SolderedElectronics/Dasduino-LITE-hardware-design/OUTPUTS/V1.2.2/Dasduino LITE Pinout.jpg

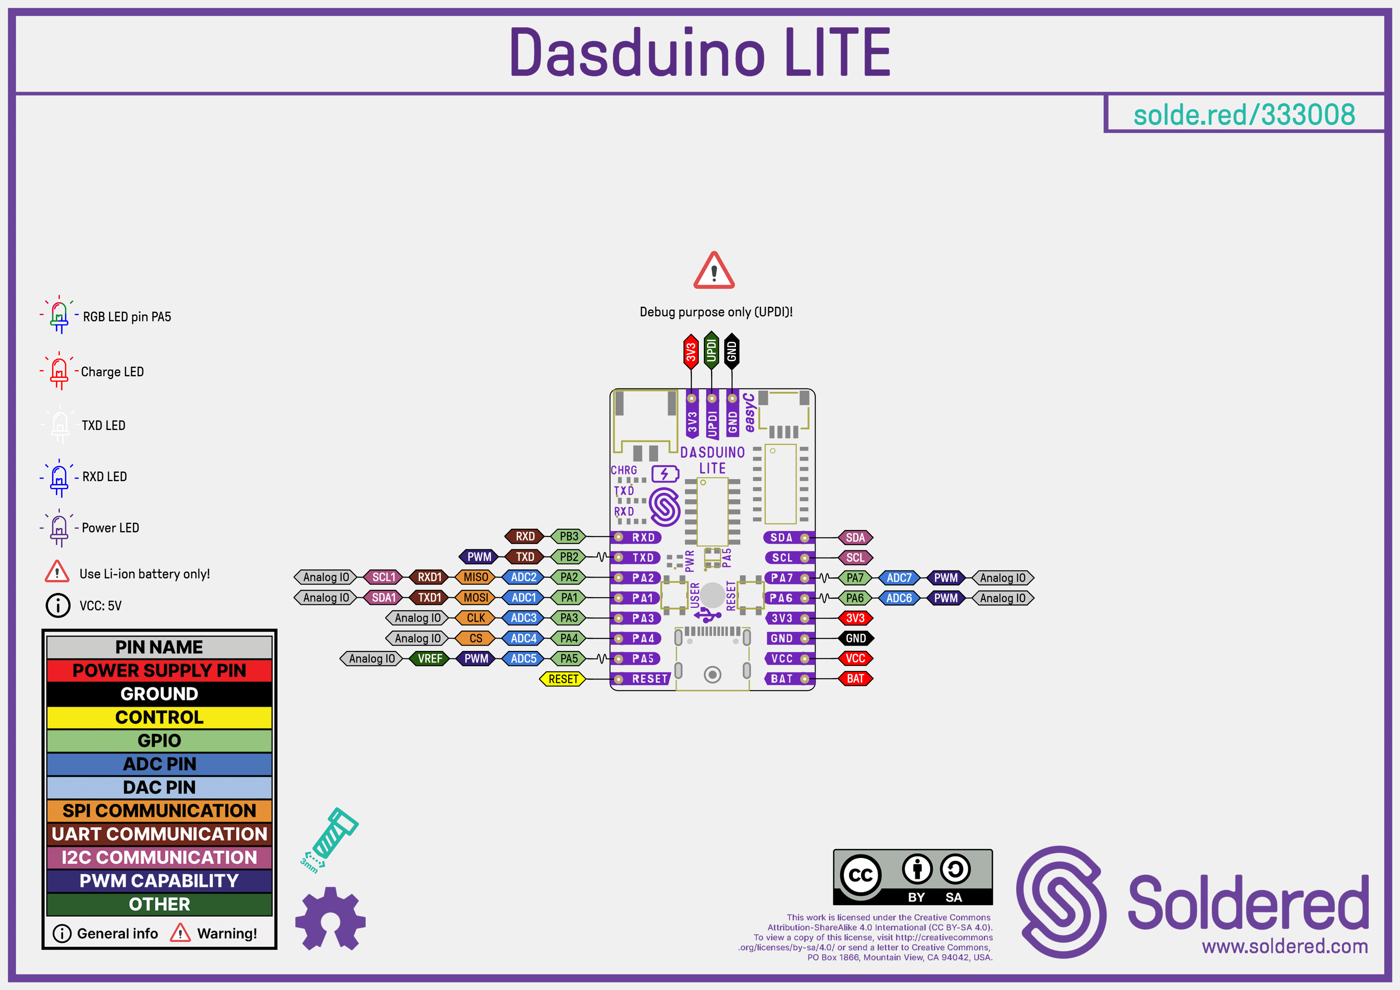
OUTPUTS/V1.2.2/Dasduino LITE Pinout.jpg
